Blinkinlabs/ch55x_programmer/releases/2023-01-09_ch55x_programmer_RevA.pdf

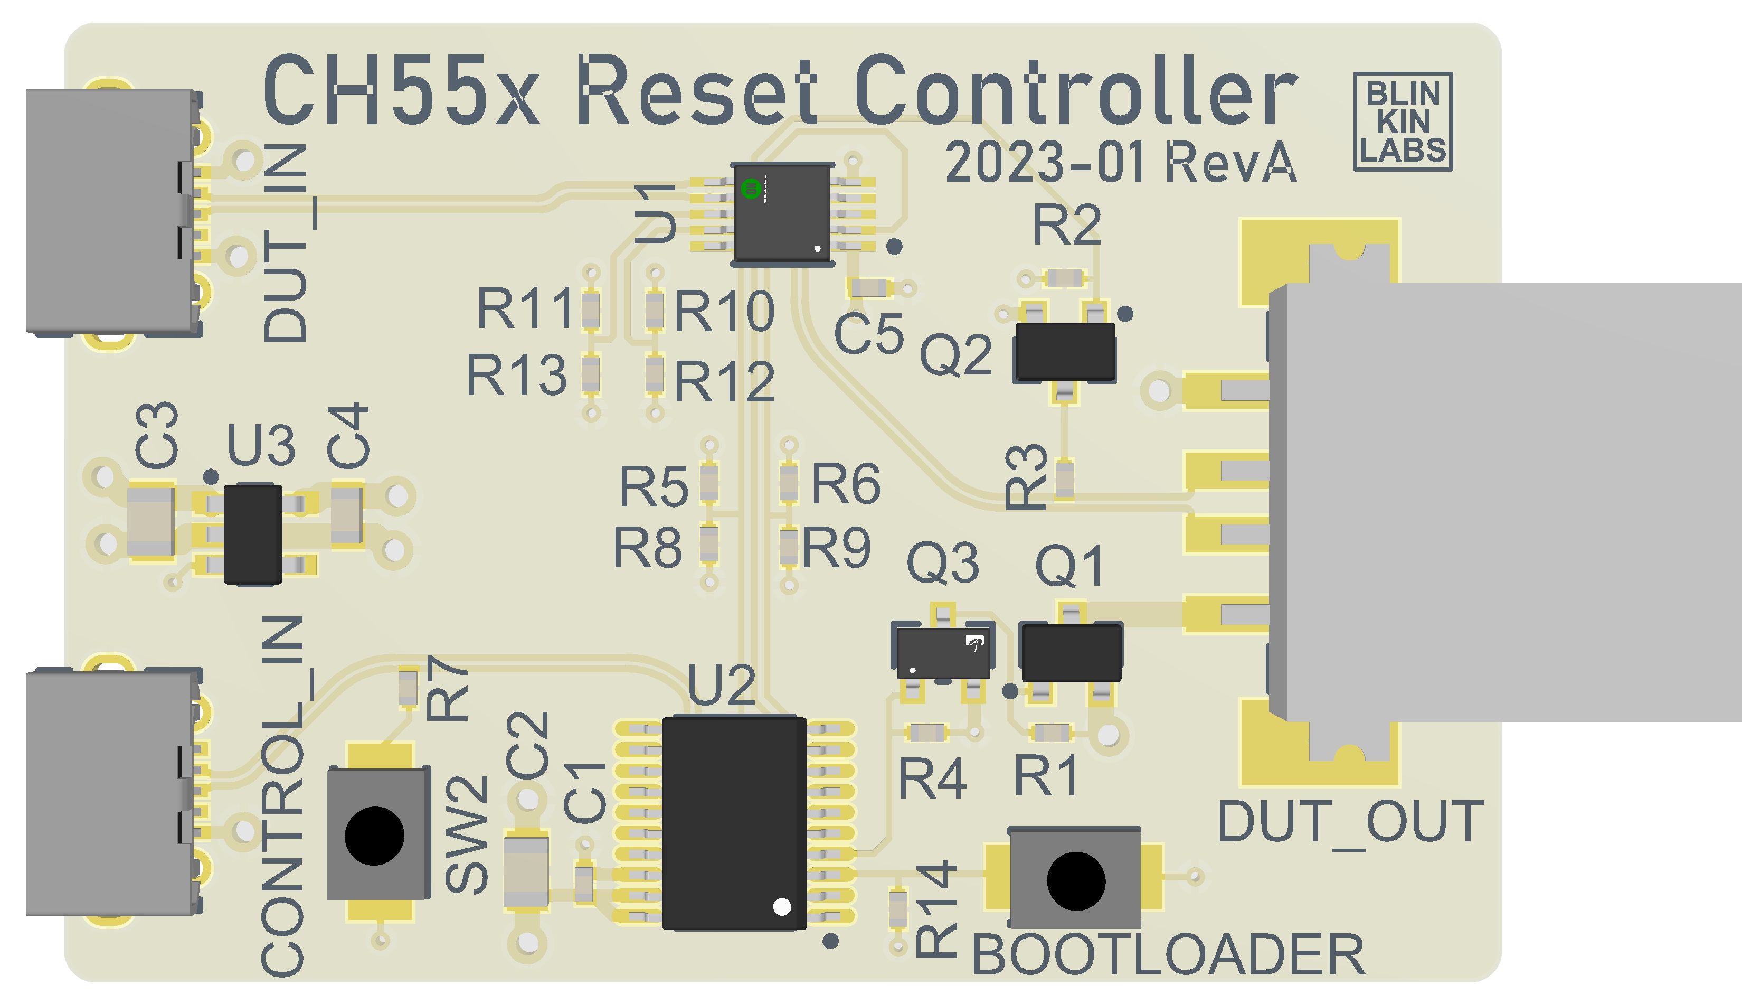
[picture p44: page 1]

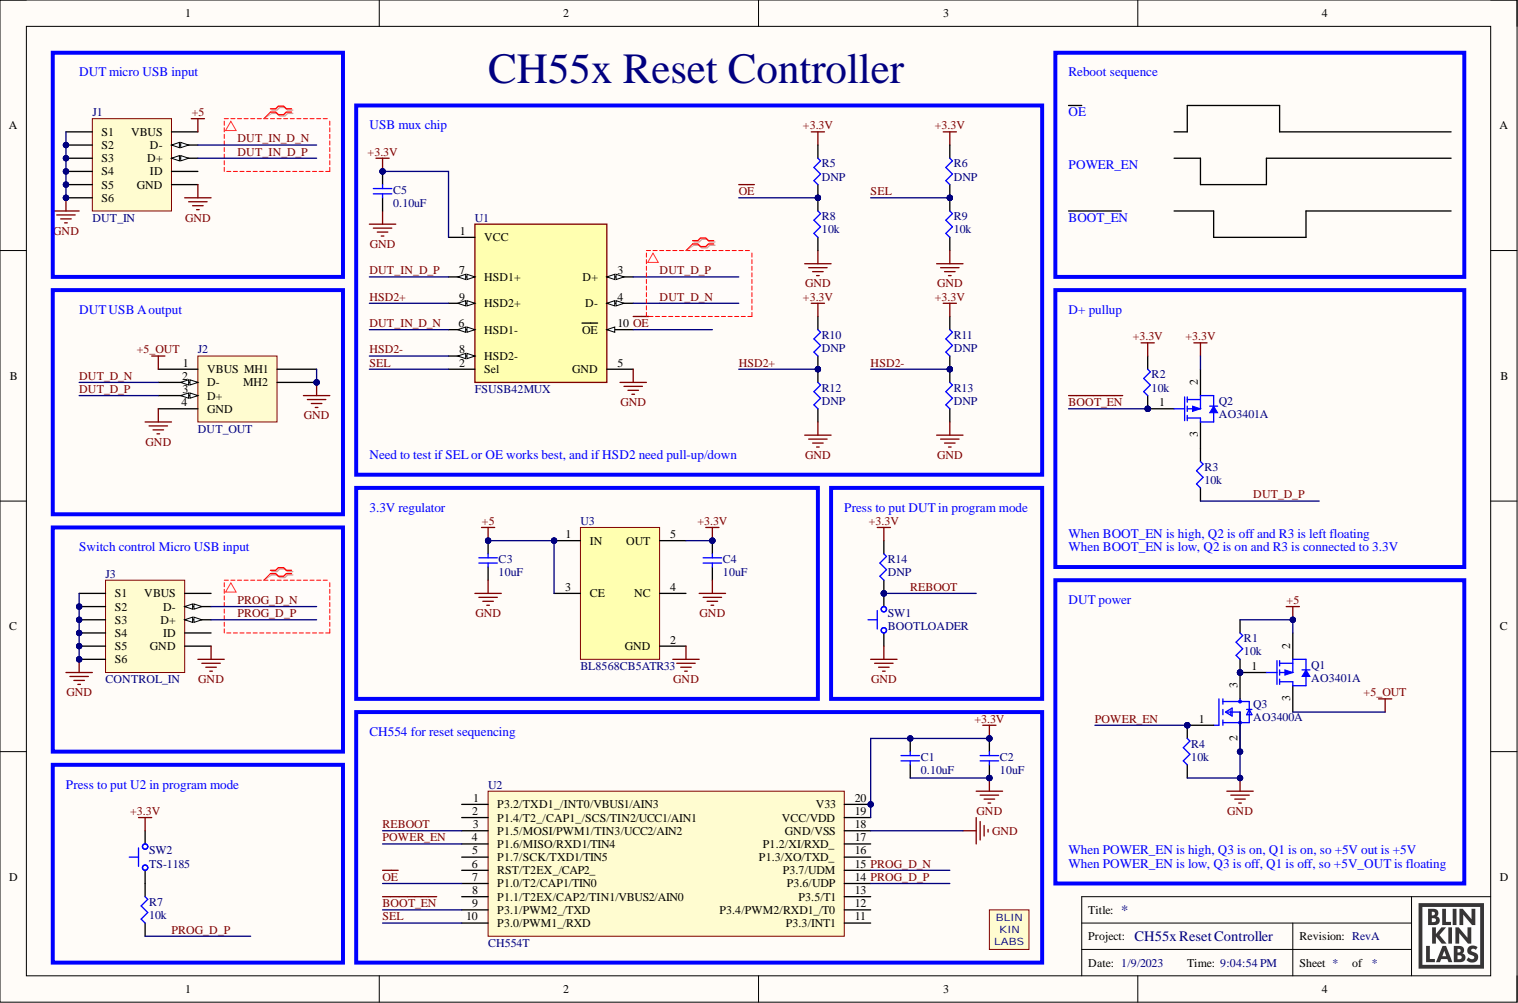
[picture p45: page 2]

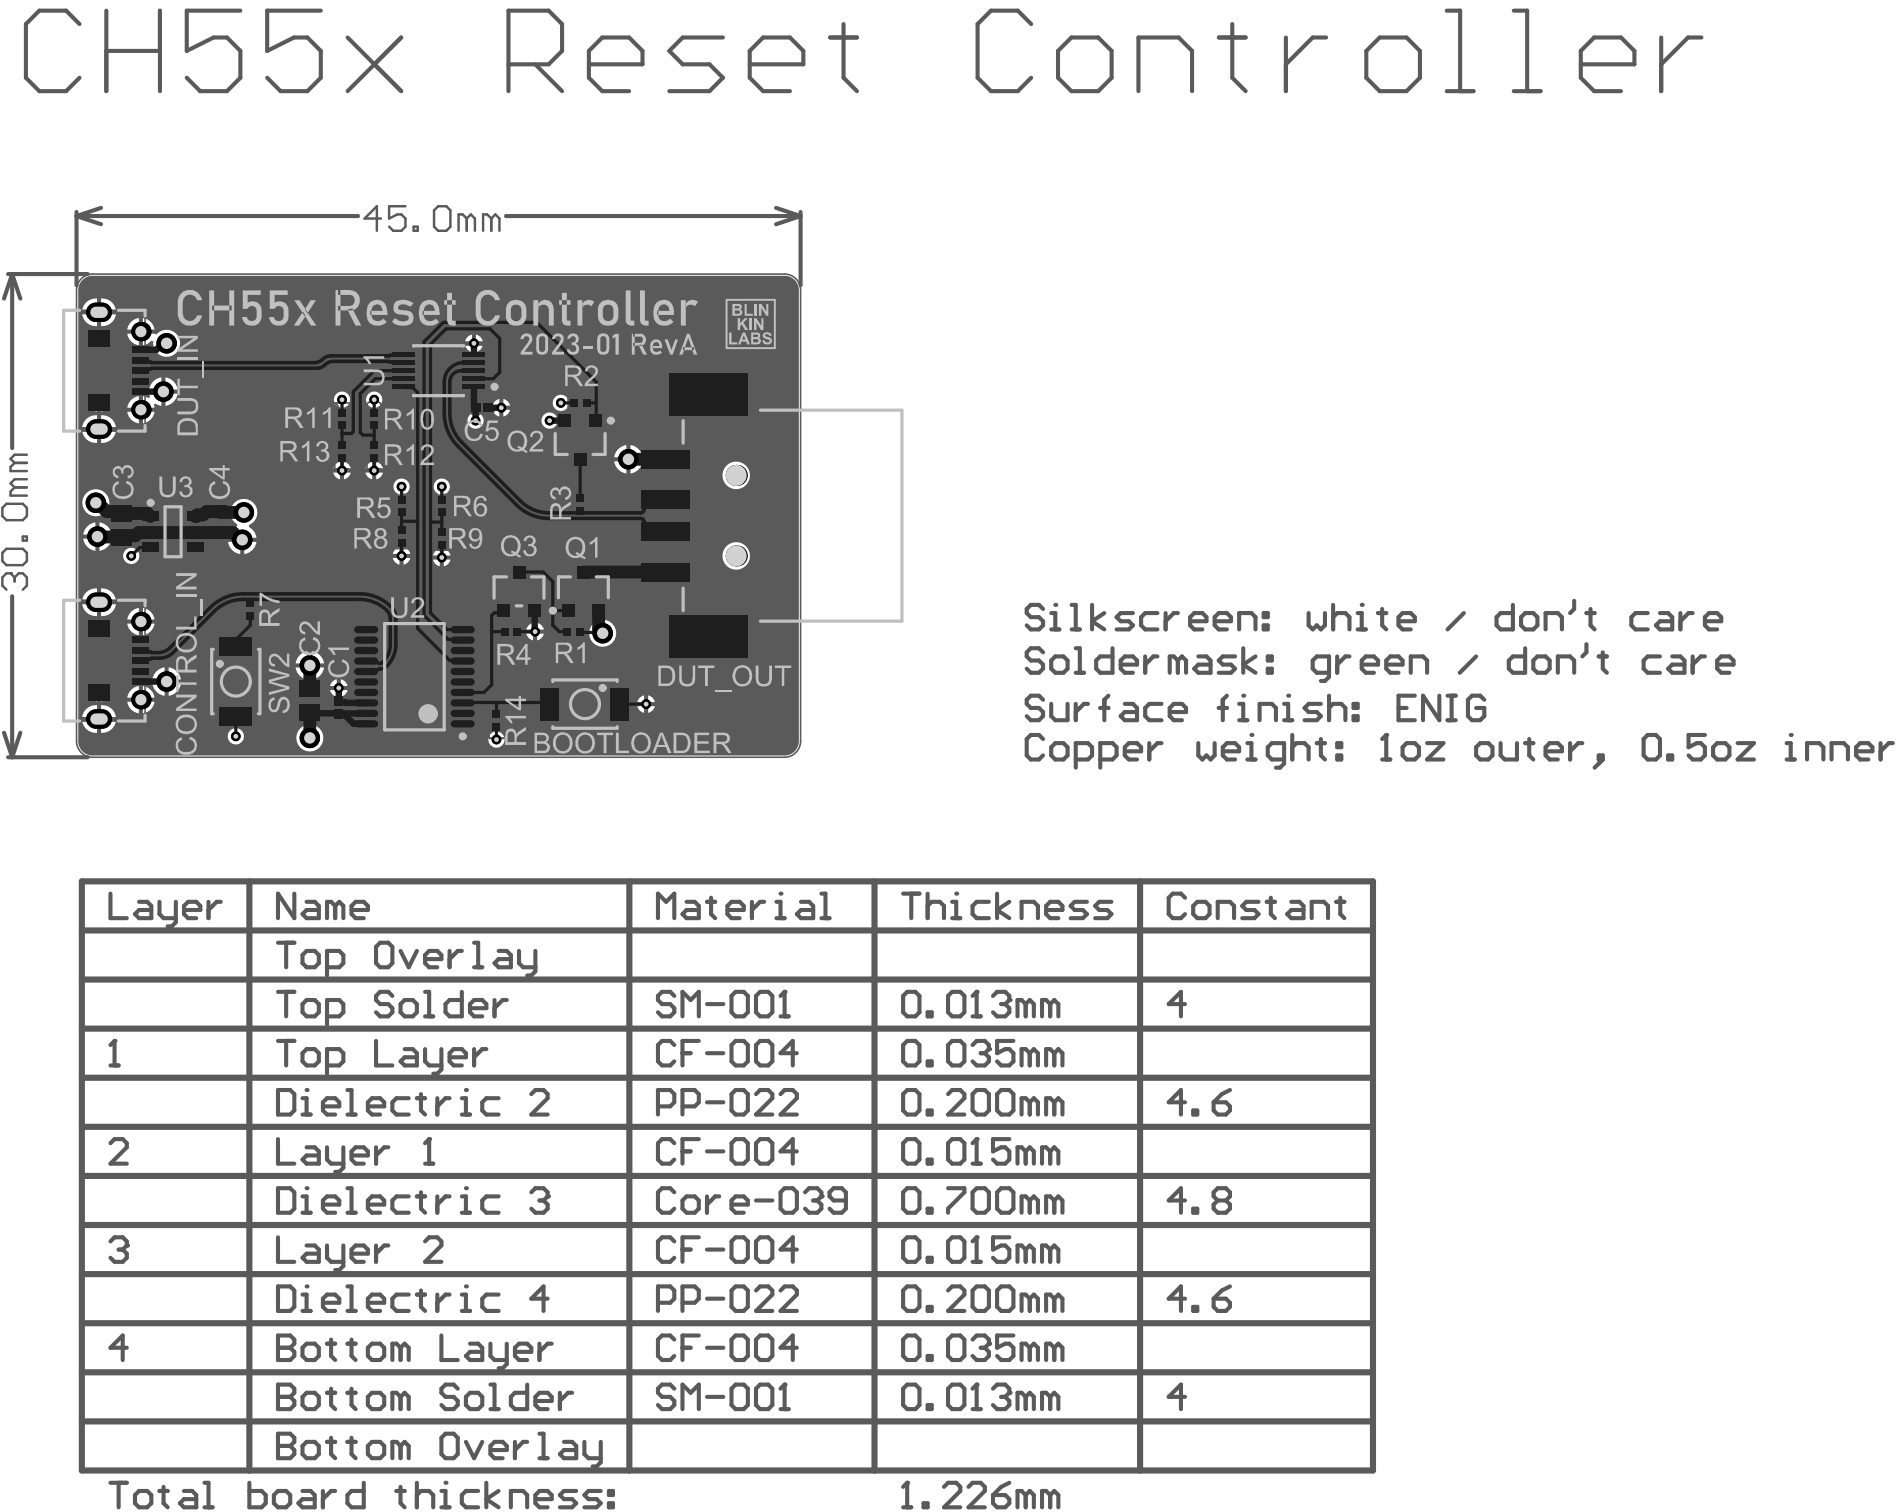
[picture p46: page 3]

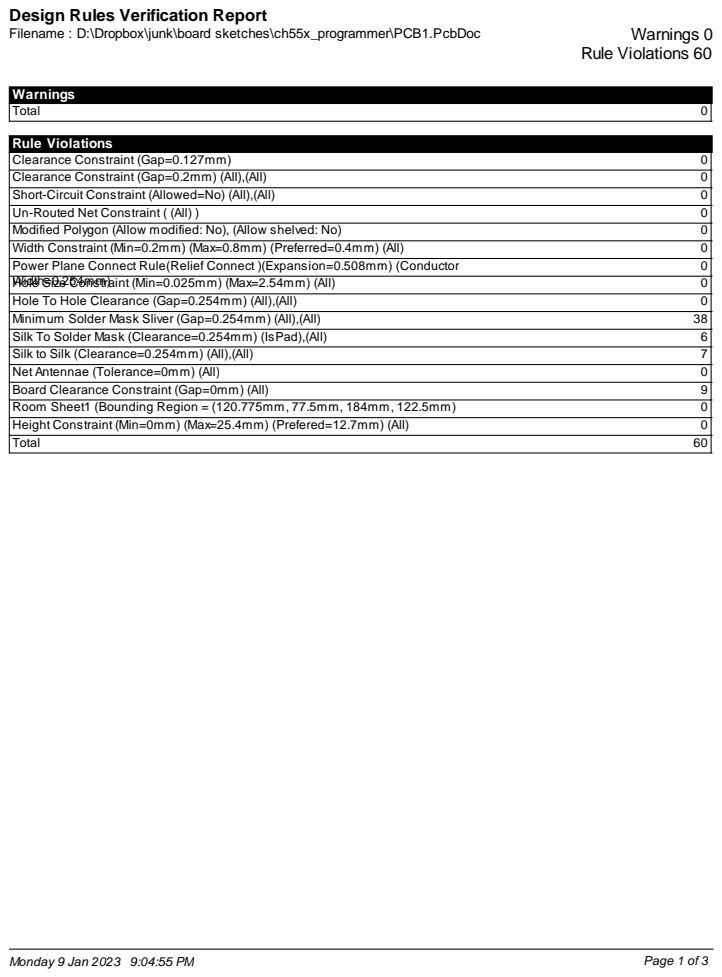
[picture p47: page 4]

Design Rules Verification Report

Rule Violations
Power Plane Connect Rule(Relief Connect )(Expansion=0.508mm) (Conductor
Width=0.254mm)

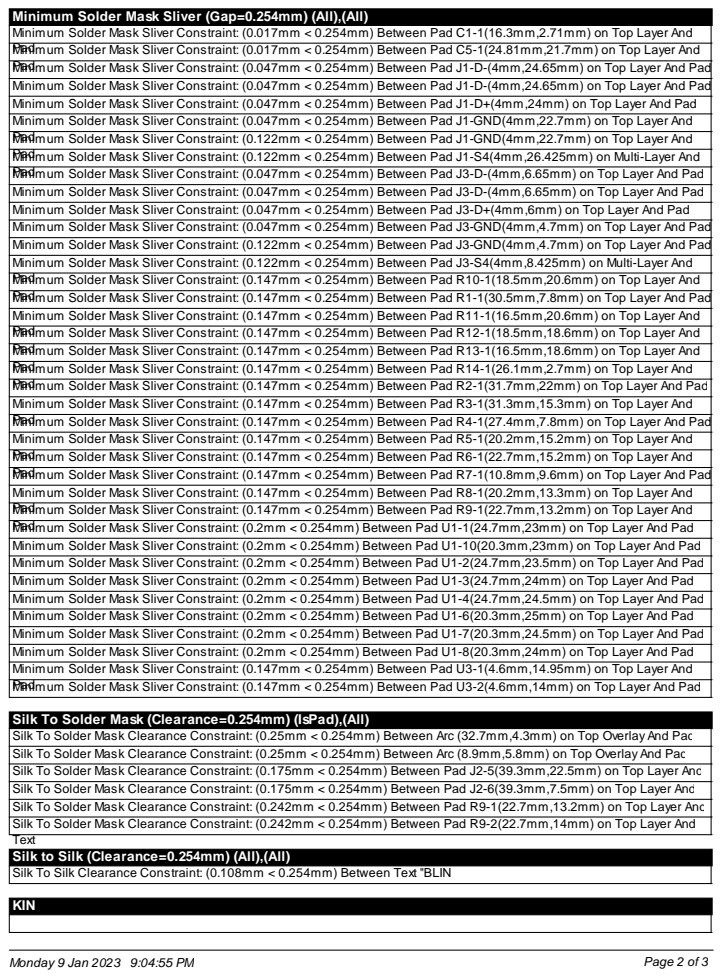
[picture p48: page 5]

Minimum Solder Mask Sliver (Gap=0.254mm) (All),(All)
Minimum Solder Mask Sliver Constraint: (0.017mm < 0.254mm) Between Pad C1-1(16.3mm,2.71mm) on Top Layer And
PaMindimum Solder Mask Sliver Constraint: (0.017mm < 0.254mm) Between Pad C5-1(24.81mm,21.7mm) on Top Layer And
PaMindimum Solder Mask Sliver Constraint: (0.047mm < 0.254mm) Between Pad J1-D-(4mm,24.65mm) on Top Layer And Pad
Minimum Solder Mask Sliver Constraint: (0.047mm < 0.254mm) Between Pad J1-D-(4mm,24.65mm) on Top Layer And Pad
Minimum Solder Mask Sliver Constraint: (0.047mm < 0.254mm) Between Pad J1-D+(4mm,24mm) on Top Layer And Pad
Minimum Solder Mask Sliver Constraint: (0.047mm < 0.254mm) Between Pad J1-GND(4mm,22.7mm) on Top Layer And
PaMindimum Solder Mask Sliver Constraint: (0.122mm < 0.254mm) Between Pad J1-GND(4mm,22.7mm) on Top Layer And
PaMindimum Solder Mask Sliver Constraint: (0.122mm < 0.254mm) Between Pad J1-S4(4mm,26.425mm) on Multi-Layer And
PaMindimum Solder Mask Sliver Constraint: (0.047mm < 0.254mm) Between Pad J3-D-(4mm,6.65mm) on Top Layer And Pad
Minimum Solder Mask Sliver Constraint: (0.047mm < 0.254mm) Between Pad J3-D-(4mm,6.65mm) on Top Layer And Pad
Minimum Solder Mask Sliver Constraint: (0.047mm < 0.254mm) Between Pad J3-D+(4mm,6mm) on Top Layer And Pad
Minimum Solder Mask Sliver Constraint: (0.047mm < 0.254mm) Between Pad J3-GND(4mm,4.7mm) on Top Layer And Pad
Minimum Solder Mask Sliver Constraint: (0.122mm < 0.254mm) Between Pad J3-GND(4mm,4.7mm) on Top Layer And Pad
Minimum Solder Mask Sliver Constraint: (0.122mm < 0.254mm) Between Pad J3-S4(4mm,8.425mm) on Multi-Layer And
PaMindimum Solder Mask Sliver Constraint: (0.147mm < 0.254mm) Between Pad R10-1(18.5mm,20.6mm) on Top Layer And
PaMindimum Solder Mask Sliver Constraint: (0.147mm < 0.254mm) Between Pad R1-1(30.5mm,7.8mm) on Top Layer And Pad
Minimum Solder Mask Sliver Constraint: (0.147mm < 0.254mm) Between Pad R11-1(16.5mm,20.6mm) on Top Layer And
PaMindimum Solder Mask Sliver Constraint: (0.147mm < 0.254mm) Between Pad R12-1(18.5mm,18.6mm) on Top Layer And
PaMindimum Solder Mask Sliver Constraint: (0.147mm < 0.254mm) Between Pad R13-1(16.5mm,18.6mm) on Top Layer And
PaMindimum Solder Mask Sliver Constraint: (0.147mm < 0.254mm) Between Pad R14-1(26.1mm,2.7mm) on Top Layer And
PaMindimum Solder Mask Sliver Constraint: (0.147mm < 0.254mm) Between Pad R2-1(31.7mm,22mm) on Top Layer And Pad
Minimum Solder Mask Sliver Constraint: (0.147mm < 0.254mm) Between Pad R3-1(31.3mm,15.3mm) on Top Layer And
PaMindimum Solder Mask Sliver Constraint: (0.147mm < 0.254mm) Between Pad R4-1(27.4mm,7.8mm) on Top Layer And Pad
Minimum Solder Mask Sliver Constraint: (0.147mm < 0.254mm) Between Pad R5-1(20.2mm,15.2mm) on Top Layer And
PaMindimum Solder Mask Sliver Constraint: (0.147mm < 0.254mm) Between Pad R6-1(22.7mm,15.2mm) on Top Layer And
PaMindimum Solder Mask Sliver Constraint: (0.147mm < 0.254mm) Between Pad R7-1(10.8mm,9.6mm) on Top Layer And Pad
Minimum Solder Mask Sliver Constraint: (0.147mm < 0.254mm) Between Pad R8-1(20.2mm,13.3mm) on Top Layer And
PaMindimum Solder Mask Sliver Constraint: (0.147mm < 0.254mm) Between Pad R9-1(22.7mm,13.2mm) on Top Layer And
PaMindimum Solder Mask Sliver Constraint: (0.2mm < 0.254mm) Between Pad U1-1(24.7mm,23mm) on Top Layer And Pad
Minimum Solder Mask Sliver Constraint: (0.2mm < 0.254mm) Between Pad U1-10(20.3mm,23mm) on Top Layer And Pad
Minimum Solder Mask Sliver Constraint: (0.2mm < 0.254mm) Between Pad U1-2(24.7mm,23.5mm) on Top Layer And Pad
Minimum Solder Mask Sliver Constraint: (0.2mm < 0.254mm) Between Pad U1-3(24.7mm,24mm) on Top Layer And Pad
Minimum Solder Mask Sliver Constraint: (0.2mm < 0.254mm) Between Pad U1-4(24.7mm,24.5mm) on Top Layer And Pad
Minimum Solder Mask Sliver Constraint: (0.2mm < 0.254mm) Between Pad U1-6(20.3mm,25mm) on Top Layer And Pad
Minimum Solder Mask Sliver Constraint: (0.2mm < 0.254mm) Between Pad U1-7(20.3mm,24.5mm) on Top Layer And Pad
Minimum Solder Mask Sliver Constraint: (0.2mm < 0.254mm) Between Pad U1-8(20.3mm,24mm) on Top Layer And Pad
Minimum Solder Mask Sliver Constraint: (0.147mm < 0.254mm) Between Pad U3-1(4.6mm,14.95mm) on Top Layer And
PaMindimum Solder Mask Sliver Constraint: (0.147mm < 0.254mm) Between Pad U3-2(4.6mm,14mm) on Top Layer And Pad

Silk To Solder Mask (Clearance=0.254mm) (IsPad),(All)
Silk To Solder Mask Clearance Constraint: (0.25mm < 0.254mm) Between Arc (32.7mm,4.3mm) on Top OverlayAnd Pad
Silk To Solder Mask Clearance Constraint: (0.25mm < 0.254mm) Between Arc (8.9mm,5.8mm) on Top OverlayAnd Pad
Silk To Solder Mask Clearance Constraint: (0.175mm < 0.254mm) Between Pad J2-5(39.3mm,22.5mm) on Top Layer And
Silk To Solder Mask Clearance Constraint: (0.175mm < 0.254mm) Between Pad J2-6(39.3mm,7.5mm) on Top Layer And
Silk To Solder Mask Clearance Constraint: (0.242mm < 0.254mm) Between Pad R9-1(22.7mm,13.2mm) on Top Layer And
Silk To Solder Mask Clearance Constraint: (0.242mm < 0.254mm) Between Pad R9-2(22.7mm,14mm) on Top Layer And
Text
Silk to Silk (Clearance=0.254mm) (All),(All)
Silk To Silk Clearance Constraint: (0.108mm < 0.254mm) Between Text "BLIN

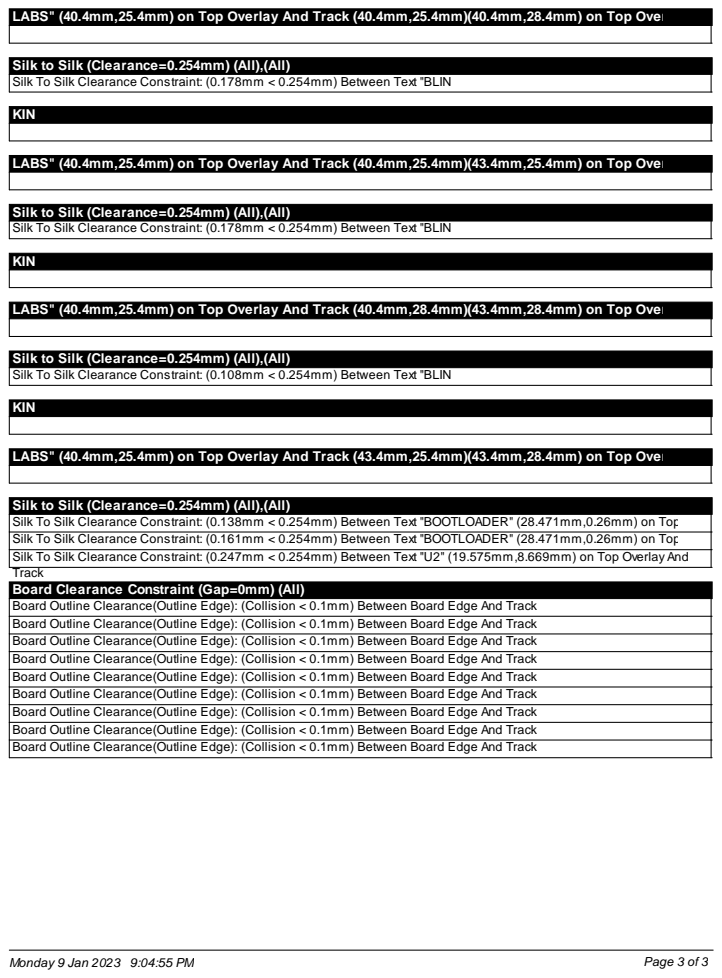
[picture p49: page 6]

LABS" (40.4mm,25.4mm) on Top Overlay And Track (40.4mm,25.4mm)(40.4mm,28.4mm) on Top Overl

Silk to Silk (Clearance=0.254mm) (All),(All)
Silk To Silk Clearance Constraint: (0.178mm < 0.254mm) Between Text "BLIN

LABS" (40.4mm,25.4mm) on Top Overlay And Track (40.4mm,25.4mm)(43.4mm,25.4mm) on Top Overl

LABS" (40.4mm,25.4mm) on Top Overlay And Track (40.4mm,28.4mm)(43.4mm,28.4mm) on Top Overl

Silk To Silk Clearance Constraint: (0.108mm < 0.254mm) Between Text "BLIN

LABS" (40.4mm,25.4mm) on Top Overlay And Track (43.4mm,25.4mm)(43.4mm,28.4mm) on Top Overl

Silk To Silk Clearance Constraint: (0.138mm < 0.254mm) Between Text "BOOTLOADER" (28.471mm,0.26mm) on Top
Silk To Silk Clearance Constraint: (0.161mm < 0.254mm) Between Text "BOOTLOADER" (28.471mm,0.26mm) on Top
Silk To Silk Clearance Constraint: (0.247mm < 0.254mm) Between Text "U2" (19.575mm,8.669mm) on Top OverlayAnd
Track
Board Clearance Constraint (Gap=0mm) (All)
Board Outline Clearance(Outline Edge): (Collision < 0.1mm) Between Board Edge And Track

### Electrical Rules Check Report

Class | Document | Message
Warning | Sheet1.SchDoc | Net O\E\ has no driving source (Pin R5-1, Pin R8-2, Pin U1-10, Pin U2-7)
Warning | Sheet1.SchDoc | Un-Designated Part L?
Monday 9 Jan 2023 9:04:56 PM | Page 1 of 1

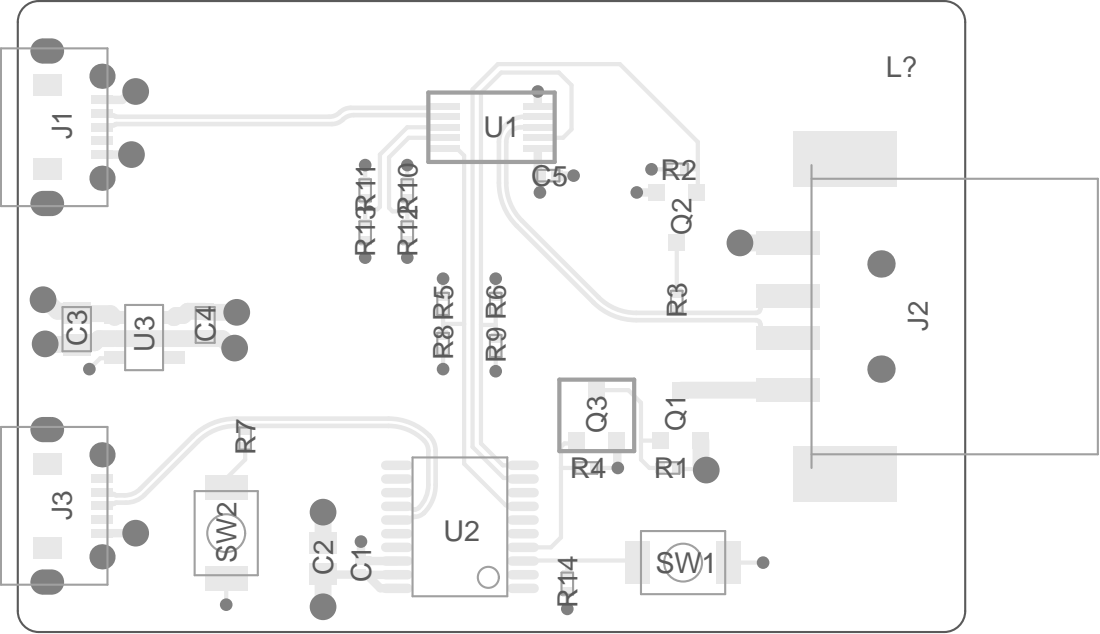
[picture p50: page 8]

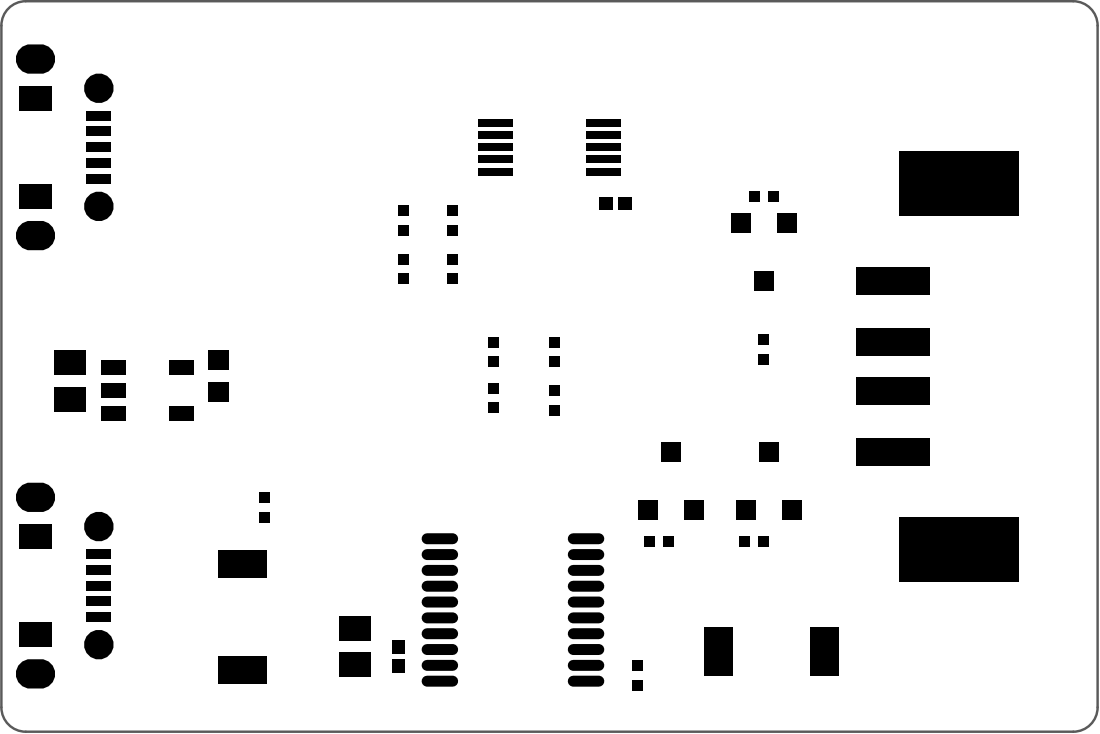
[picture p51: page 9]
